nickbild/artemis/img/youtube.png

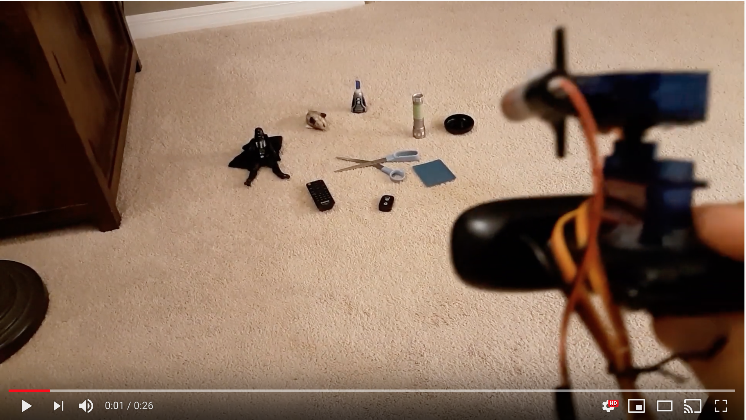
img/youtube.png
